geronimogonzalez/andino-jazzy/andino_description/docs/robot_rviz.png

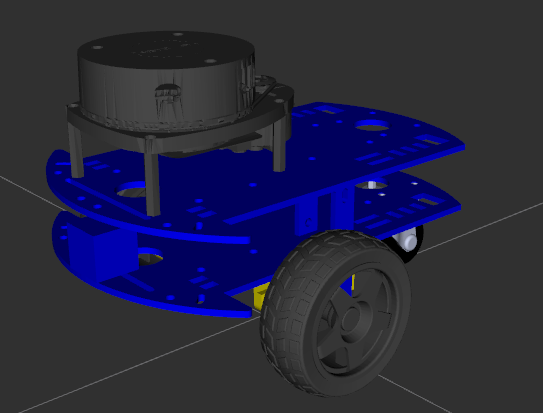
andino_description/docs/robot_rviz.png
