geronimogonzalez/andino-jazzy/navigation2/doc/requirements/images/Command-Pipeline-Support.png

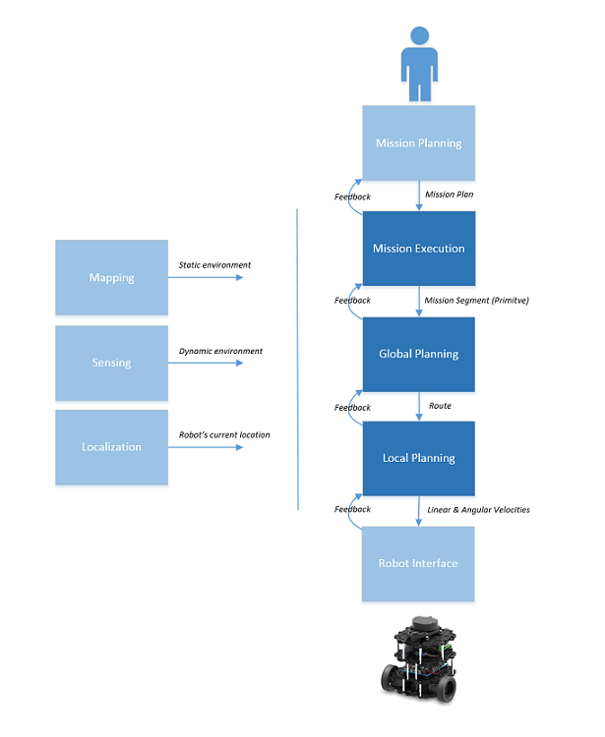
navigation2/doc/requirements/images/Command-Pipeline-Support.png
