geronimogonzalez/andino-jazzy/navigation2/doc/requirements/images/Context.png

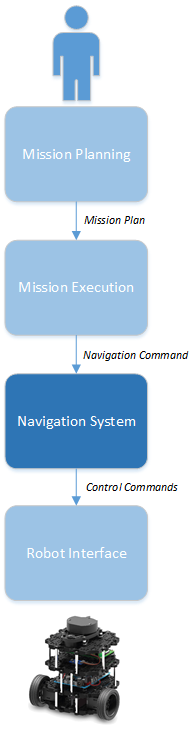
navigation2/doc/requirements/images/Context.png
