geronimogonzalez/andino-jazzy/navigation2/doc/requirements/images/Mapping-Use-Cases.png

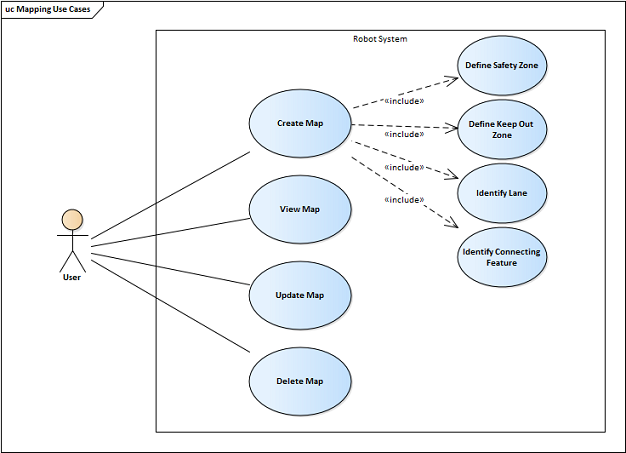
navigation2/doc/requirements/images/Mapping-Use-Cases.png
