geronimogonzalez/andino-jazzy/navigation2/doc/requirements/images/With-Support-Modules.png

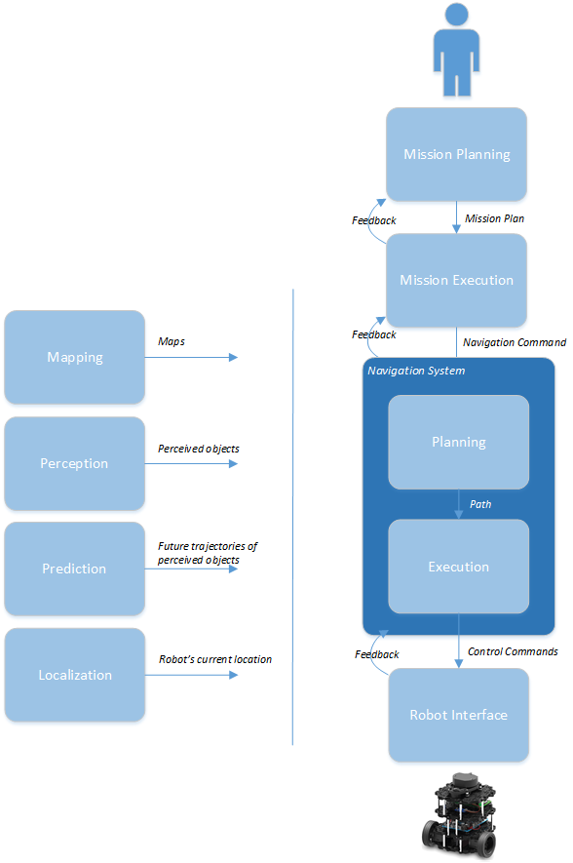
navigation2/doc/requirements/images/With-Support-Modules.png
