geronimogonzalez/andino-jazzy/navigation2/doc/sponsors_feb_2024.png

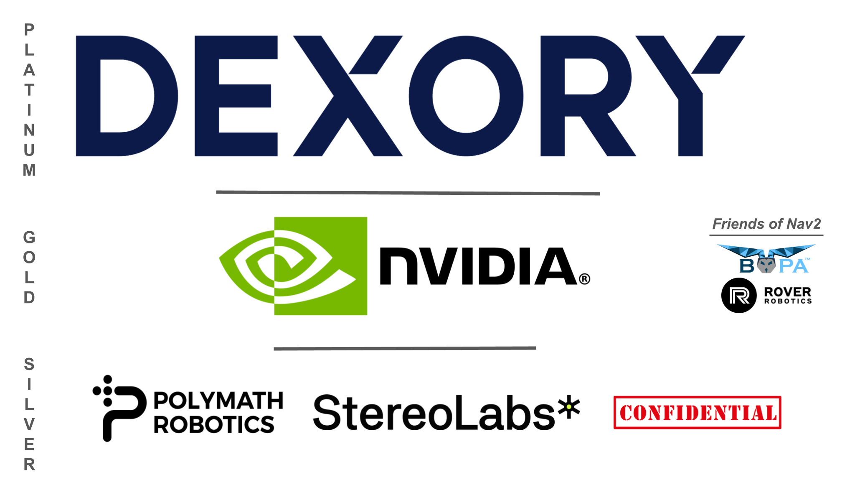
navigation2/doc/sponsors_feb_2024.png
