geronimogonzalez/andino-jazzy/navigation2/doc/sponsors_jan_2024.png

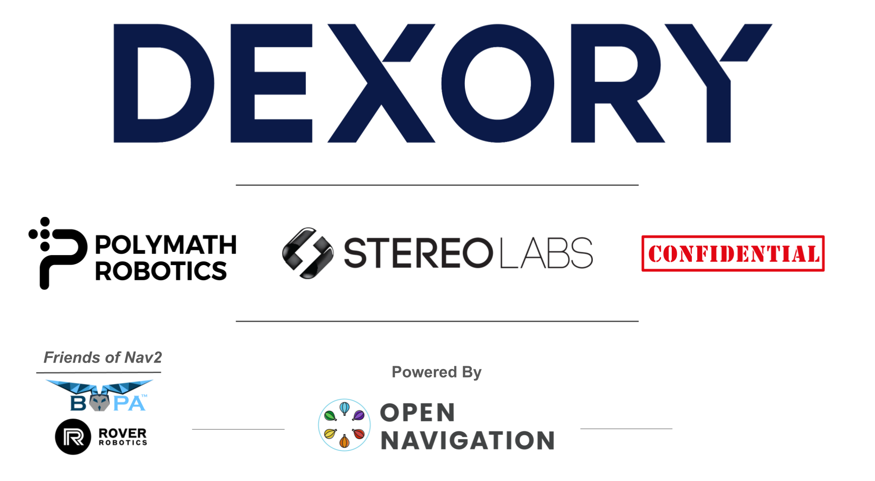
navigation2/doc/sponsors_jan_2024.png
