geronimogonzalez/andino-jazzy/navigation2/doc/sponsors_may_2023.png

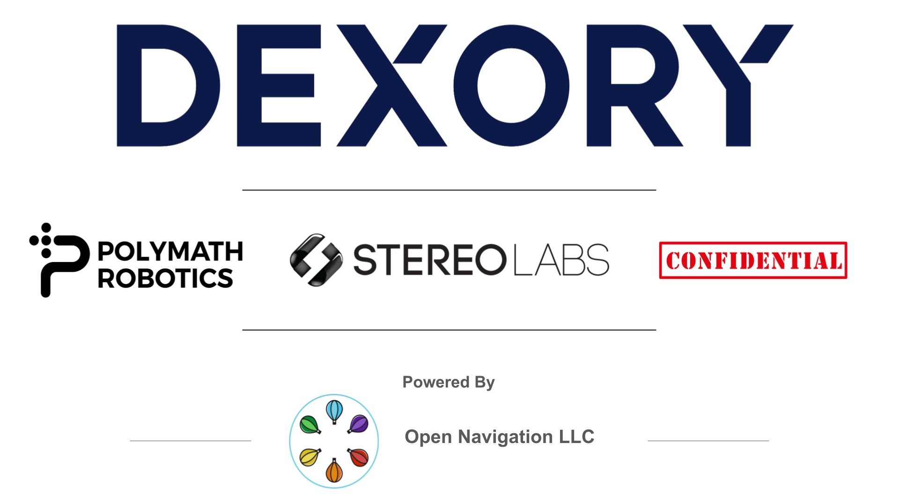
navigation2/doc/sponsors_may_2023.png
