geronimogonzalez/andino-jazzy/navigation2/nav2_bt_navigator/doc/follow_point.png

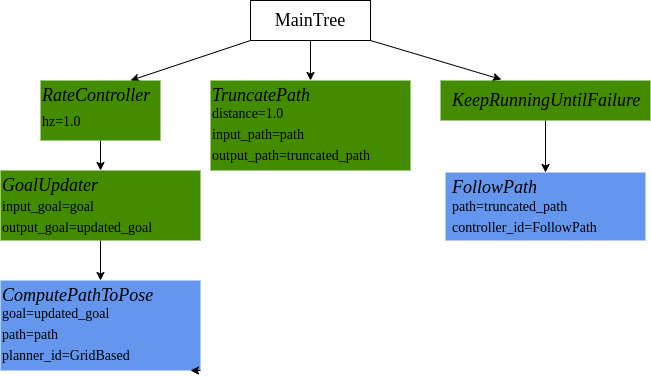
navigation2/nav2_bt_navigator/doc/follow_point.png
