geronimogonzalez/andino-jazzy/navigation2/nav2_bt_navigator/doc/legend.png

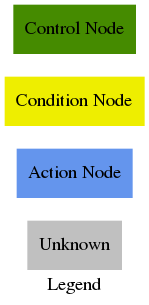
navigation2/nav2_bt_navigator/doc/legend.png
