geronimogonzalez/andino-jazzy/navigation2/nav2_bt_navigator/doc/navigate_w_replanning_distance.png

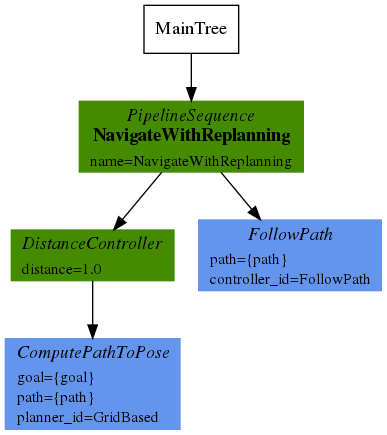
navigation2/nav2_bt_navigator/doc/navigate_w_replanning_distance.png
