geronimogonzalez/andino-jazzy/navigation2/nav2_bt_navigator/doc/parallel_w_goal_patience_and_recovery.png

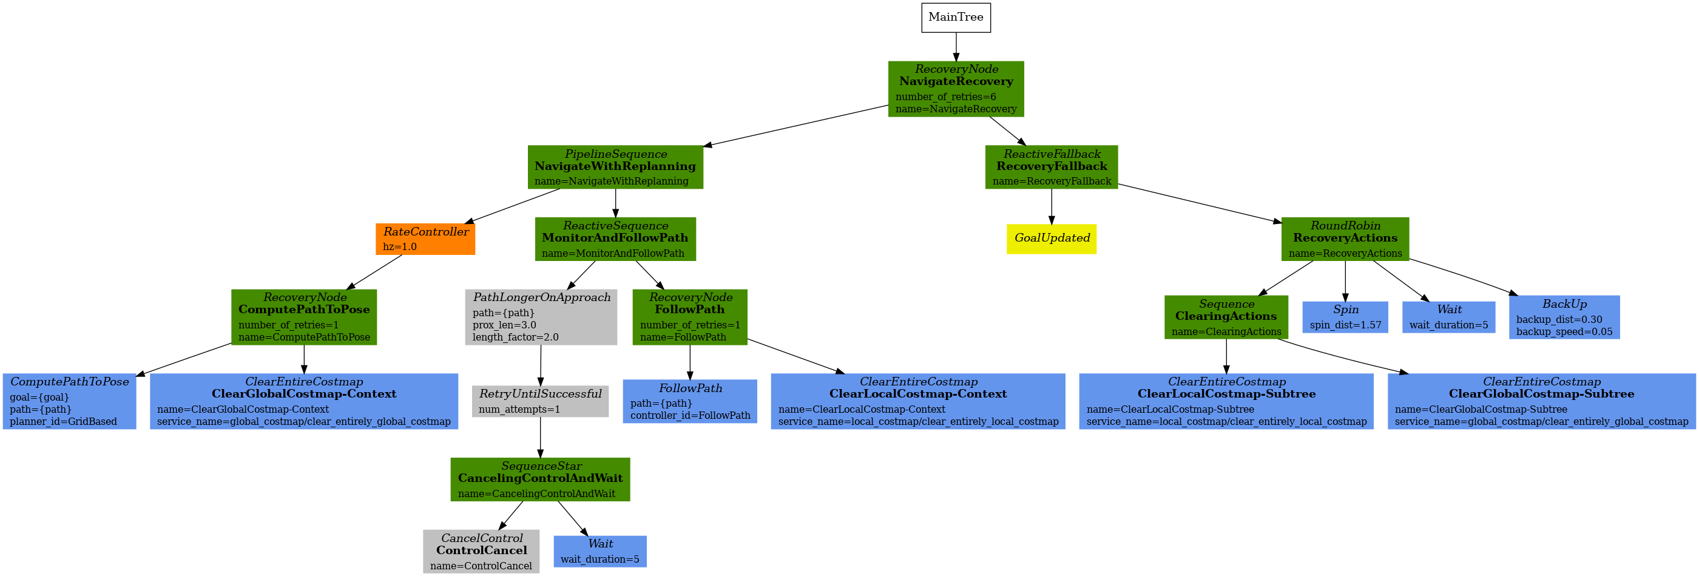
navigation2/nav2_bt_navigator/doc/parallel_w_goal_patience_and_recovery.png
