geronimogonzalez/andino-jazzy/navigation2/nav2_bt_navigator/doc/parallel_w_recovery.png

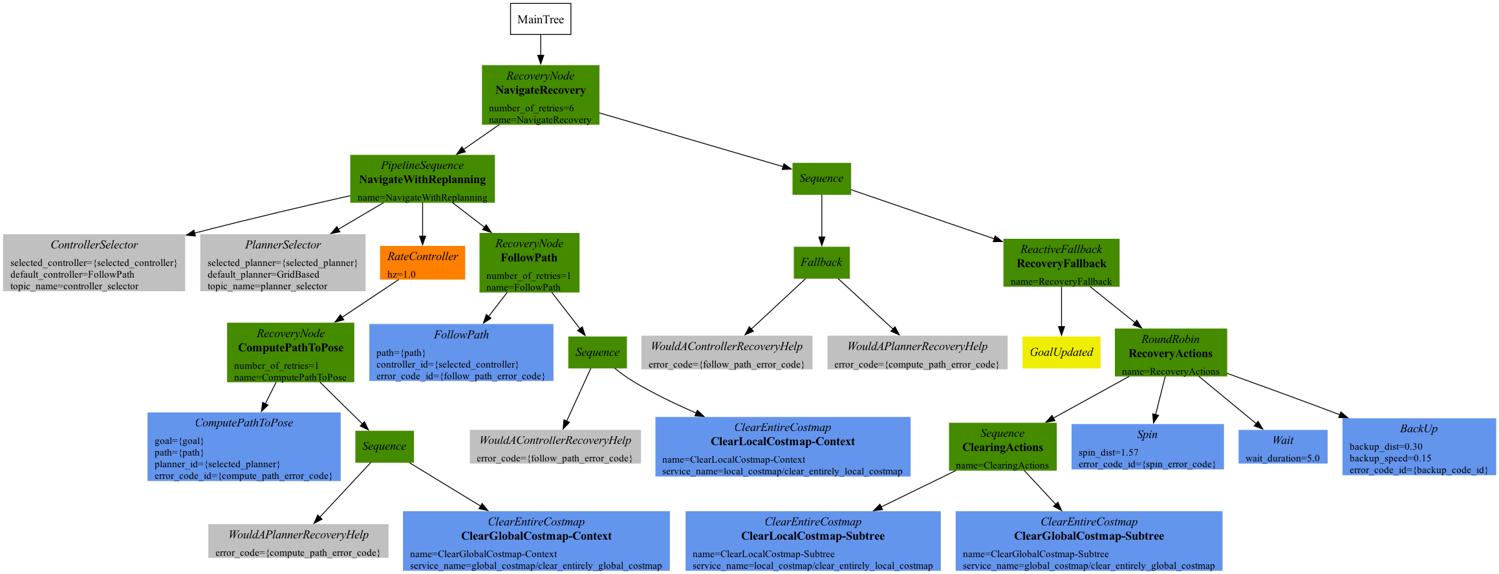
navigation2/nav2_bt_navigator/doc/parallel_w_recovery.png
