geronimogonzalez/andino-jazzy/navigation2/nav2_bt_navigator/doc/recovery_node.png

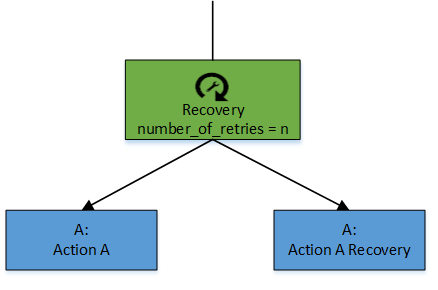
navigation2/nav2_bt_navigator/doc/recovery_node.png
