geronimogonzalez/andino-jazzy/navigation2/nav2_bt_navigator/doc/recovery_w_goal_updated.png

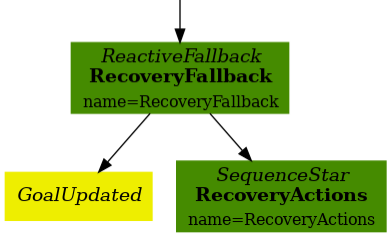
navigation2/nav2_bt_navigator/doc/recovery_w_goal_updated.png
