geronimogonzalez/andino-jazzy/navigation2/nav2_collision_monitor/doc/cm_ros_devday.png

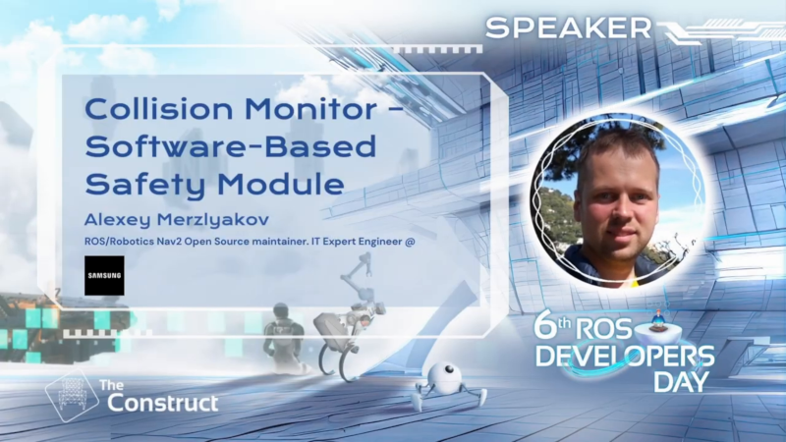
navigation2/nav2_collision_monitor/doc/cm_ros_devday.png
