geronimogonzalez/andino-jazzy/navigation2/nav2_collision_monitor/doc/HLD.png

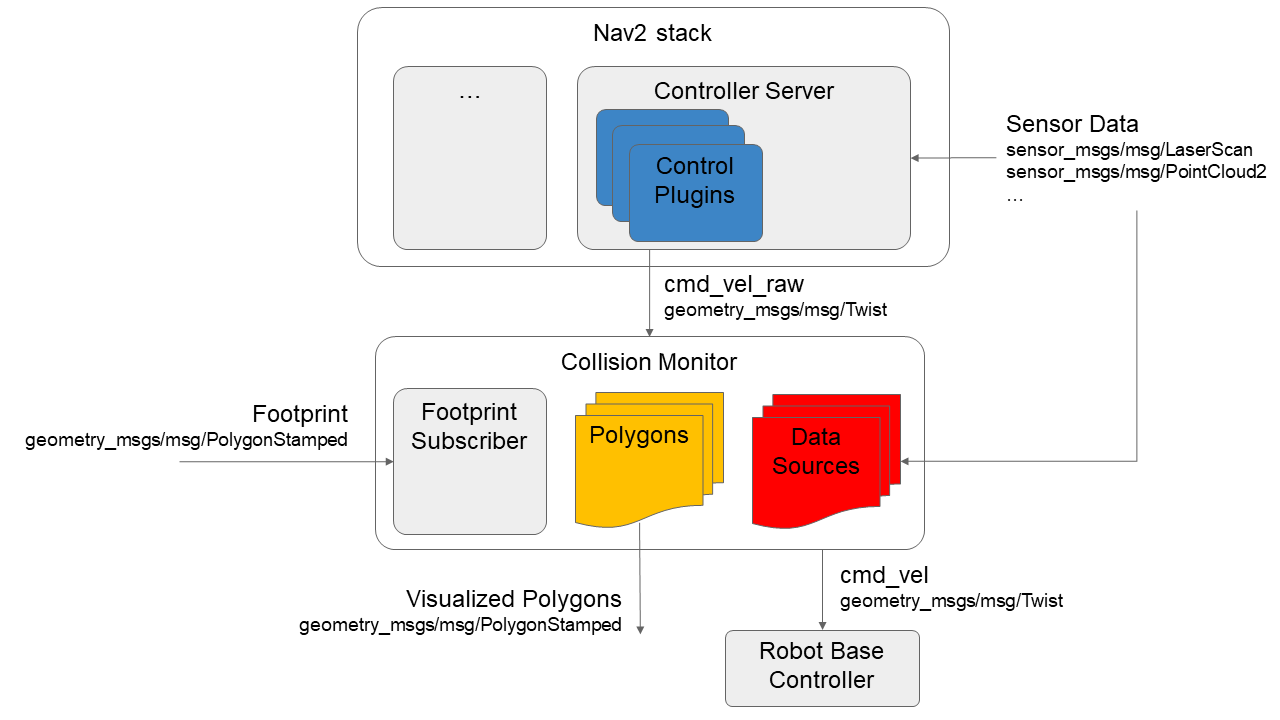
navigation2/nav2_collision_monitor/doc/HLD.png
