geronimogonzalez/andino-jazzy/navigation2/nav2_collision_monitor/doc/polygons.png

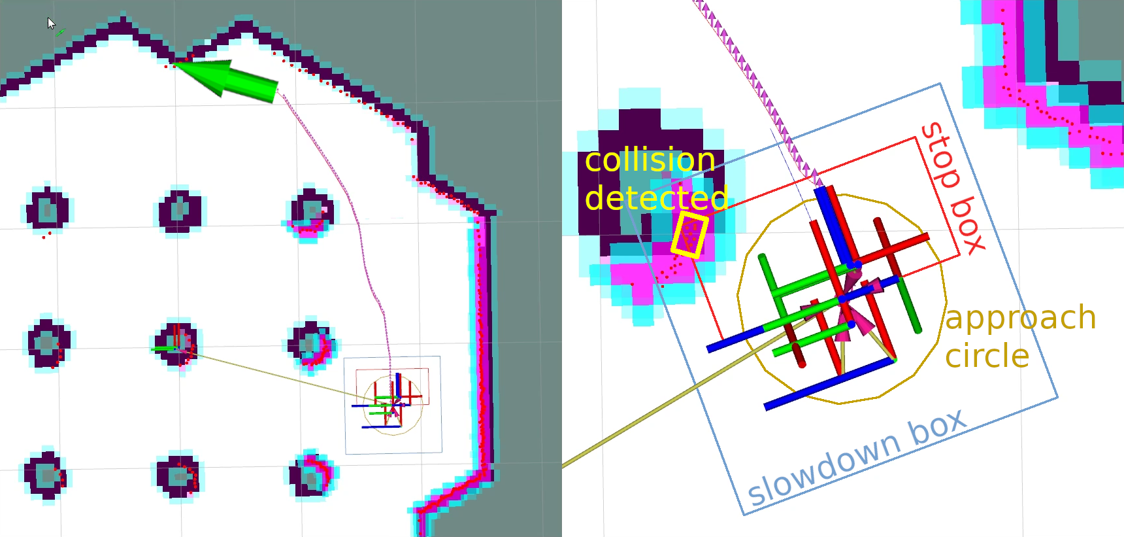
navigation2/nav2_collision_monitor/doc/polygons.png
