geronimogonzalez/andino-jazzy/navigation2/nav2_docking/docs/nv_on.png

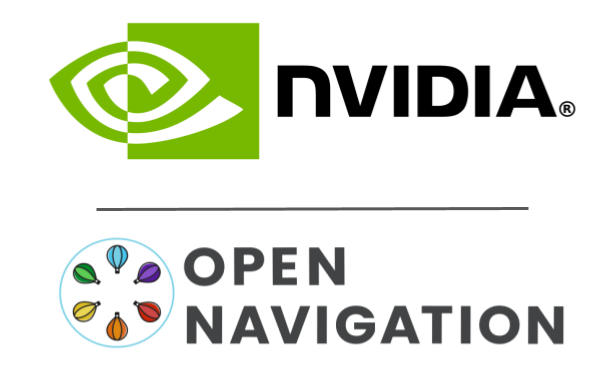
navigation2/nav2_docking/docs/nv_on.png
