geronimogonzalez/andino-jazzy/navigation2/nav2_graceful_controller/doc/trajectories.png

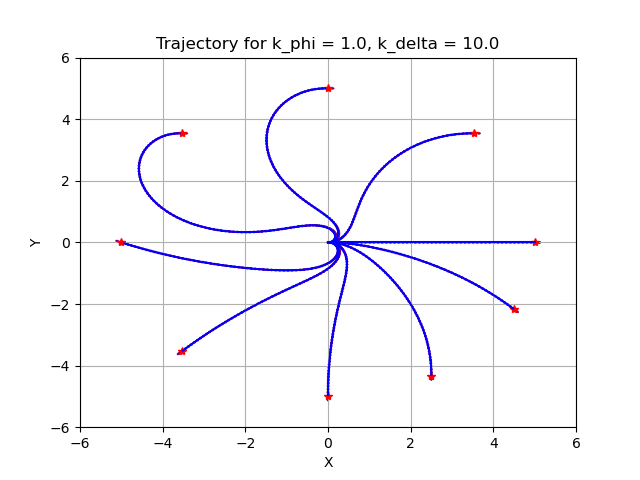
navigation2/nav2_graceful_controller/doc/trajectories.png
