geronimogonzalez/andino-jazzy/navigation2/nav2_lifecycle_manager/doc/uml_lifecycle_manager.JPG

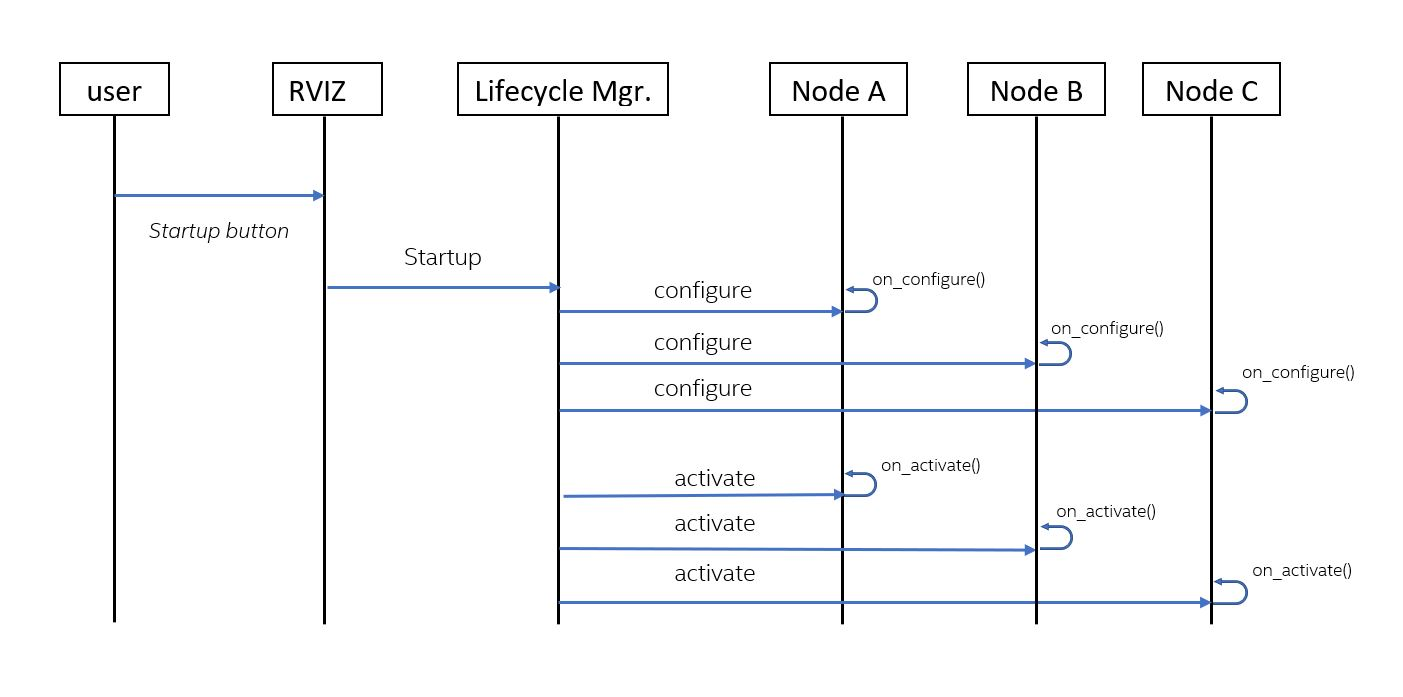
navigation2/nav2_lifecycle_manager/doc/uml_lifecycle_manager.JPG
