geronimogonzalez/andino-jazzy/navigation2/nav2_regulated_pure_pursuit_controller/doc/lookahead_algorithm.png

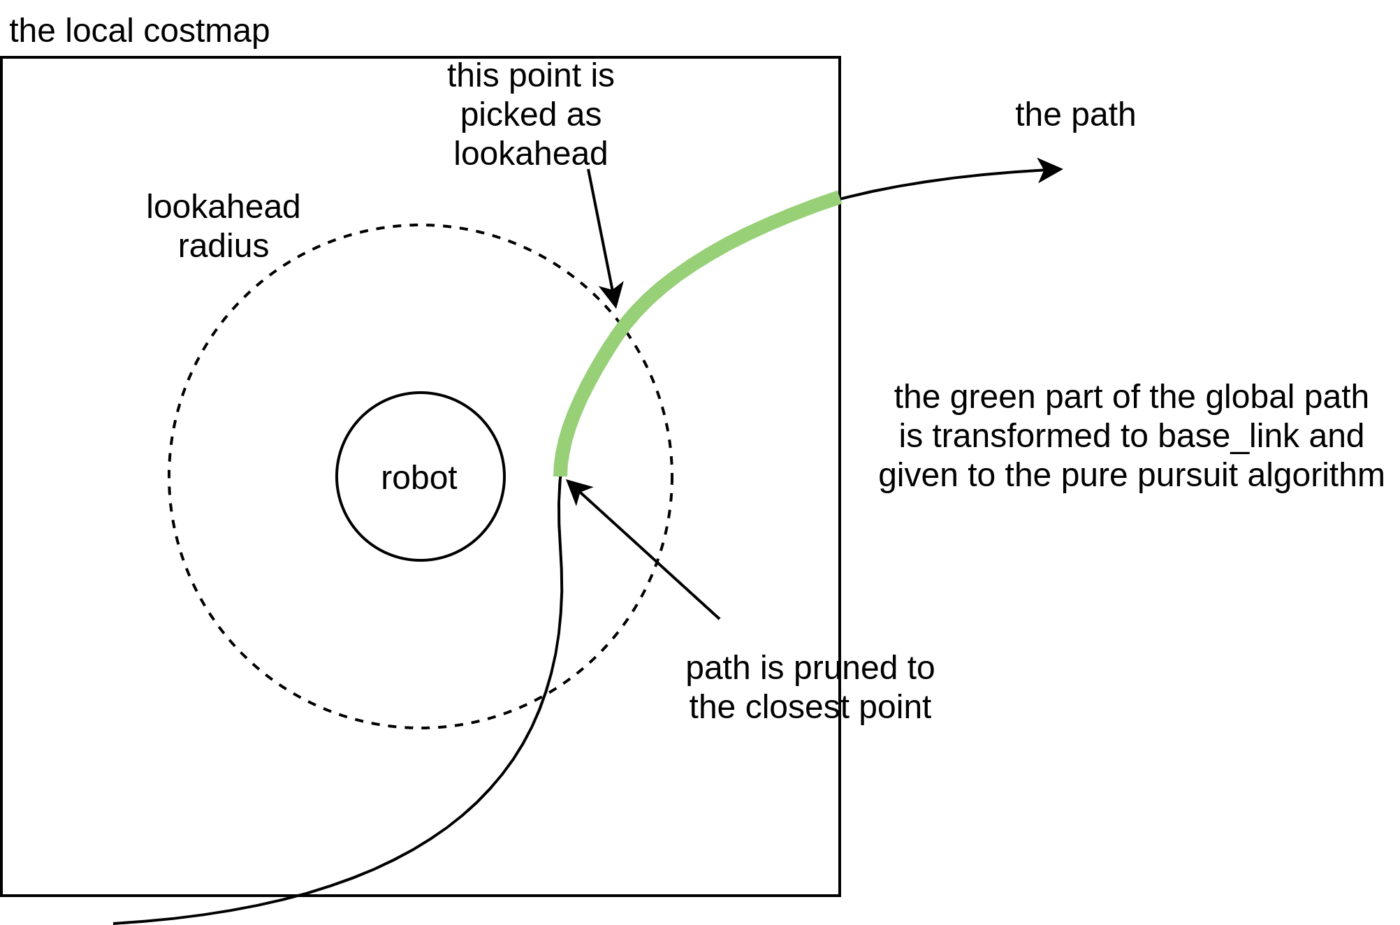
navigation2/nav2_regulated_pure_pursuit_controller/doc/lookahead_algorithm.png
