geronimogonzalez/andino-jazzy/navigation2/nav2_smac_planner/lattice_primitives/docs/all_trajectories.png

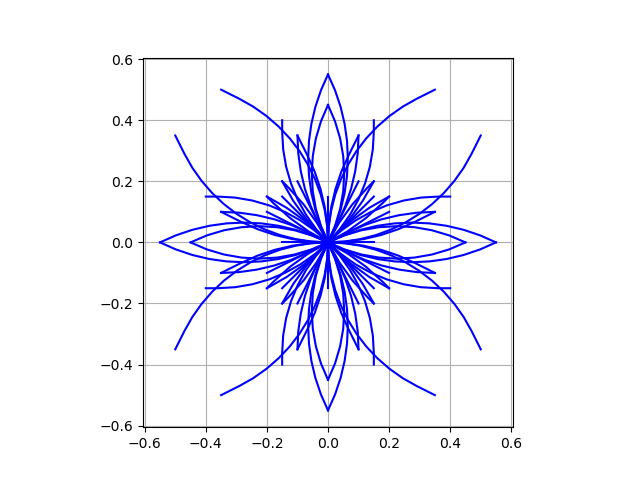
navigation2/nav2_smac_planner/lattice_primitives/docs/all_trajectories.png
