geronimogonzalez/andino-jazzy/navigation2/nav2_smac_planner/lattice_primitives/docs/angle_discretization.png

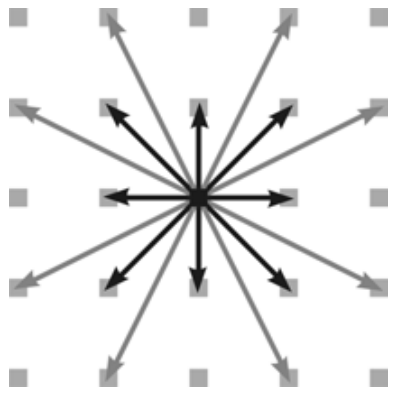
navigation2/nav2_smac_planner/lattice_primitives/docs/angle_discretization.png
