geronimogonzalez/andino-jazzy/navigation2/nav2_smac_planner/lattice_primitives/sample_primitives/5cm_resolution/1m_turning_radius/all_trajectories.png

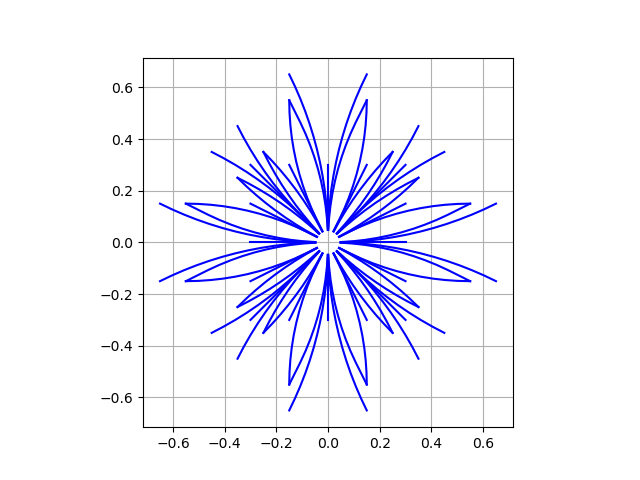
navigation2/nav2_smac_planner/lattice_primitives/sample_primitives/5cm_resolution/1m_turning_radius/all_trajectories.png
