geronimogonzalez/andino-jazzy/navigation2/nav2_smac_planner/media/A.png

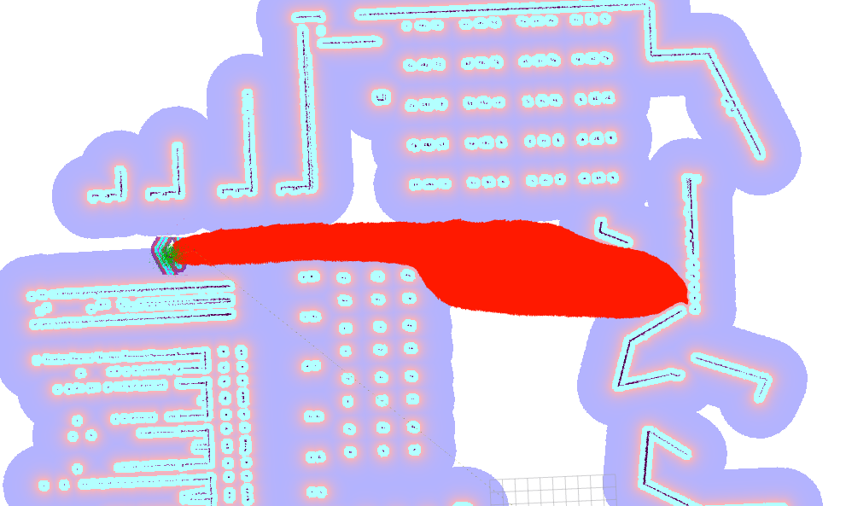
navigation2/nav2_smac_planner/media/A.png
