geronimogonzalez/andino-jazzy/navigation2/nav2_smac_planner/media/B.png

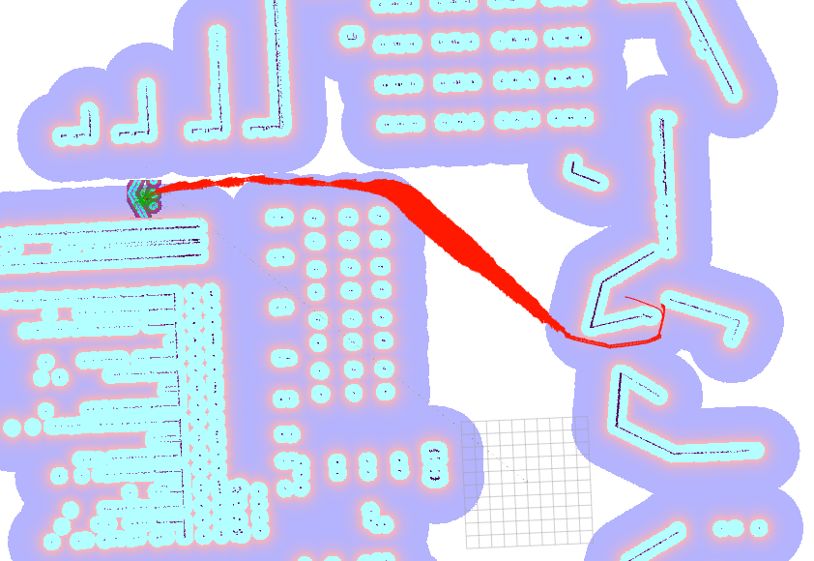
navigation2/nav2_smac_planner/media/B.png
