geronimogonzalez/andino-jazzy/navigation2/nav2_theta_star_planner/img/00-37.png

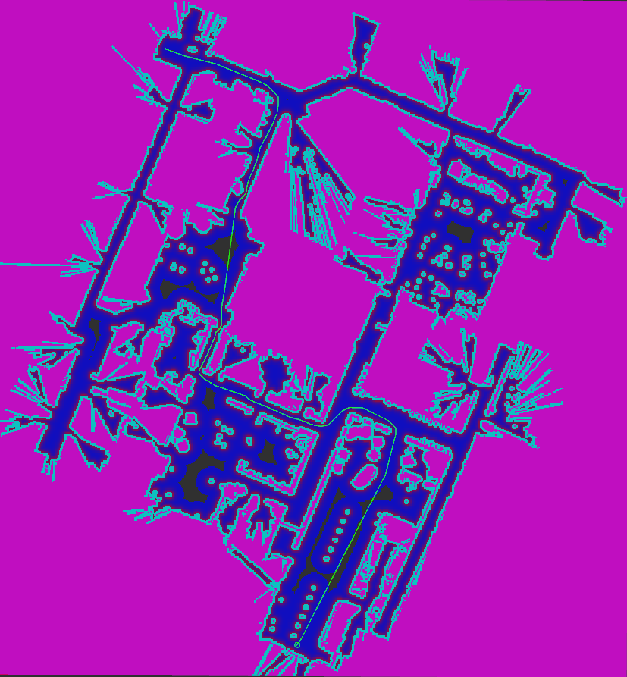
navigation2/nav2_theta_star_planner/img/00-37.png
