geronimogonzalez/andino-jazzy/andino_description/meshes/andino/chassis.stl

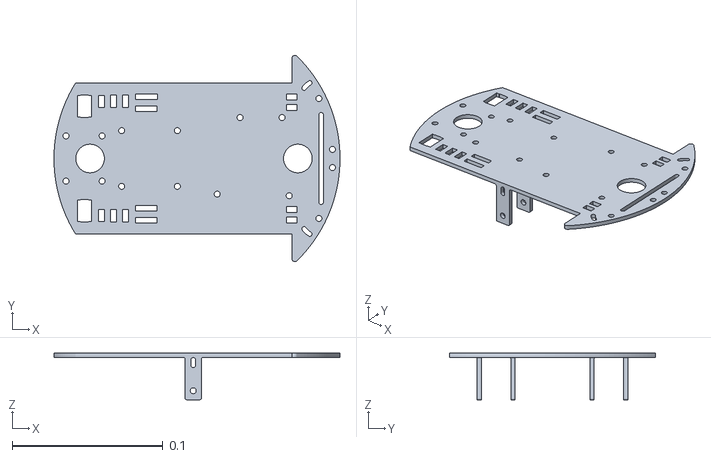
[picture p65: CAD file, 2025-10-09]
andino_description/meshes/andino/chassis.stl
0.19 x 0.137 x 0.0309
