geronimogonzalez/andino-jazzy/andino_description/meshes/andino/caster_wheel.stl

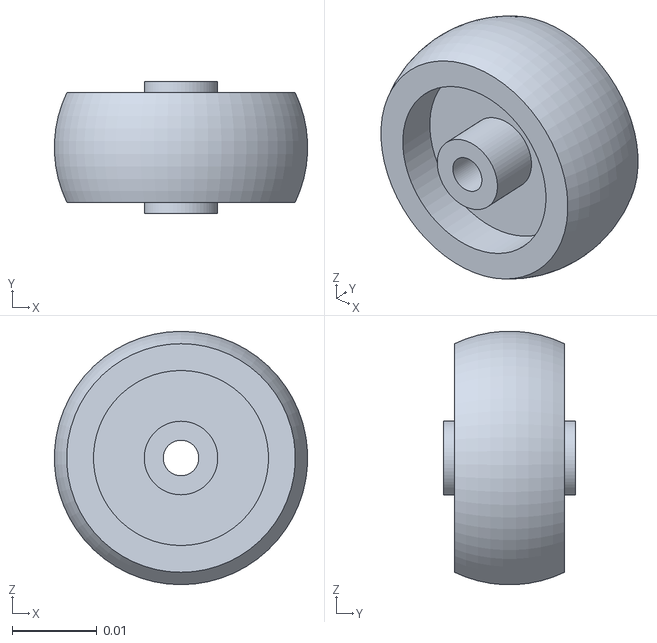
[picture p66: CAD file, 2025-10-09]
andino_description/meshes/andino/caster_wheel.stl
0.0299 x 0.0156 x 0.03
