geronimogonzalez/andino-jazzy/navigation2/nav2_costmap_2d/test/unit/keepout_filter_test.jpg

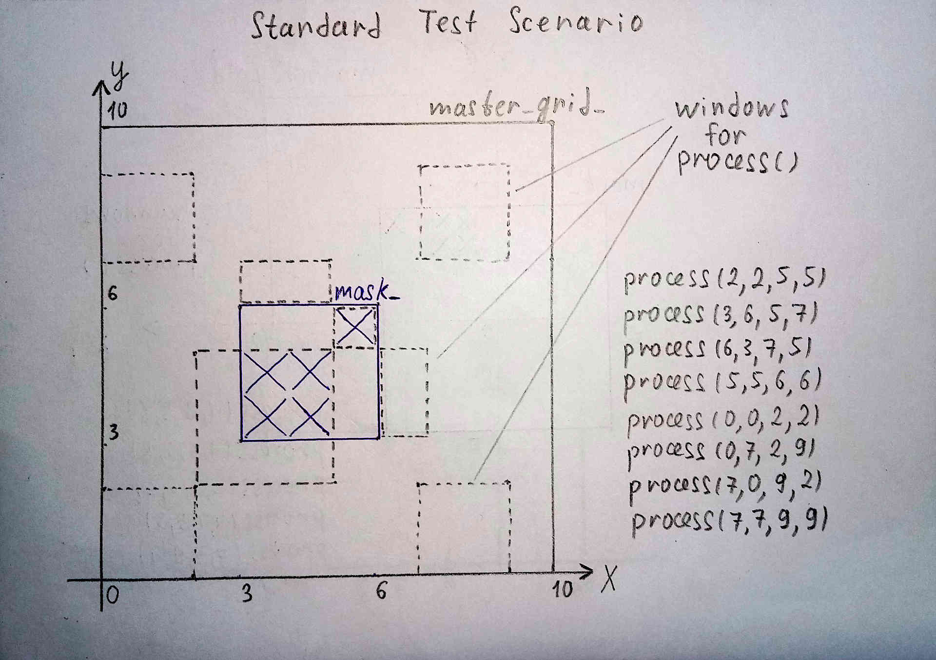
navigation2/nav2_costmap_2d/test/unit/keepout_filter_test.jpg
