geronimogonzalez/andino-jazzy/navigation2/nav2_smac_planner/test/3planners.png

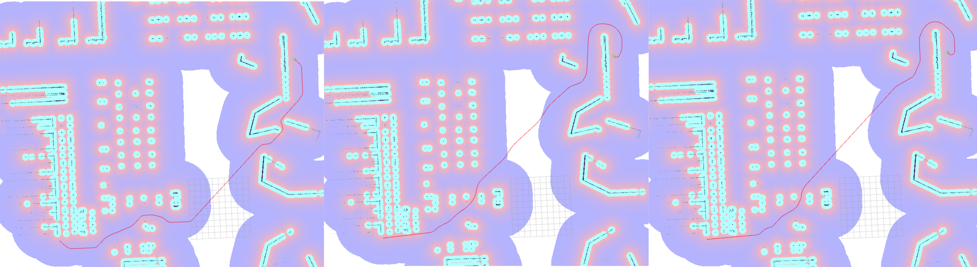
navigation2/nav2_smac_planner/test/3planners.png
