geronimogonzalez/andino-jazzy/navigation2/nav2_smac_planner/test/path.png

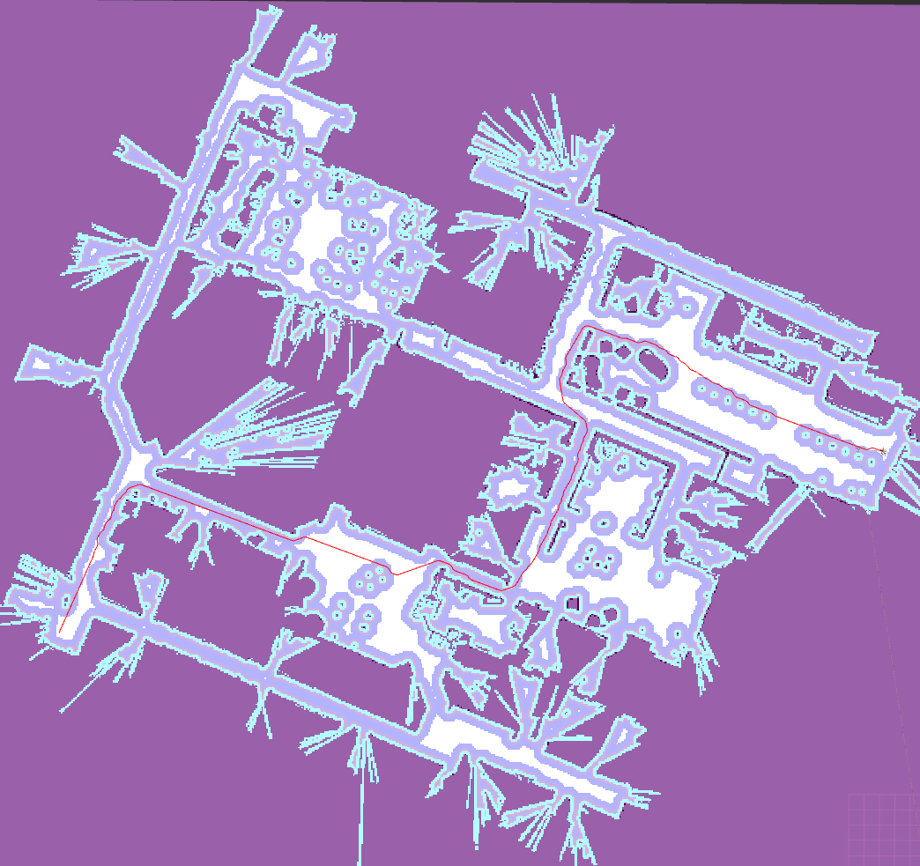
navigation2/nav2_smac_planner/test/path.png
