geronimogonzalez/andino-jazzy/navigation2/nav2_system_tests/maps/empty_room.png

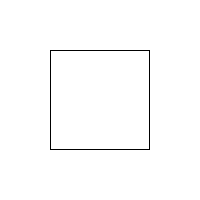
navigation2/nav2_system_tests/maps/empty_room.png
