geronimogonzalez/andino-jazzy/navigation2/nav2_system_tests/src/costmap_filters/keepout_plan.png

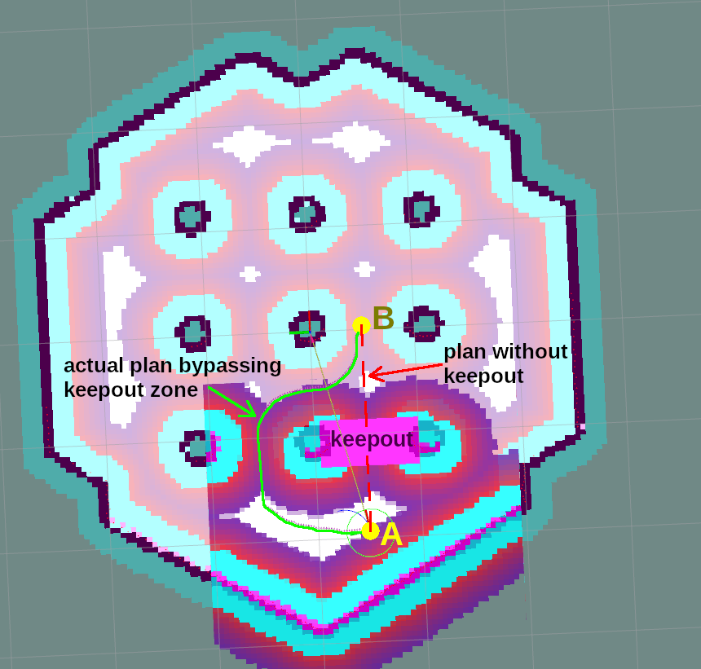
navigation2/nav2_system_tests/src/costmap_filters/keepout_plan.png
