geronimogonzalez/andino-jazzy/navigation2/nav2_system_tests/src/planning/example_result.png

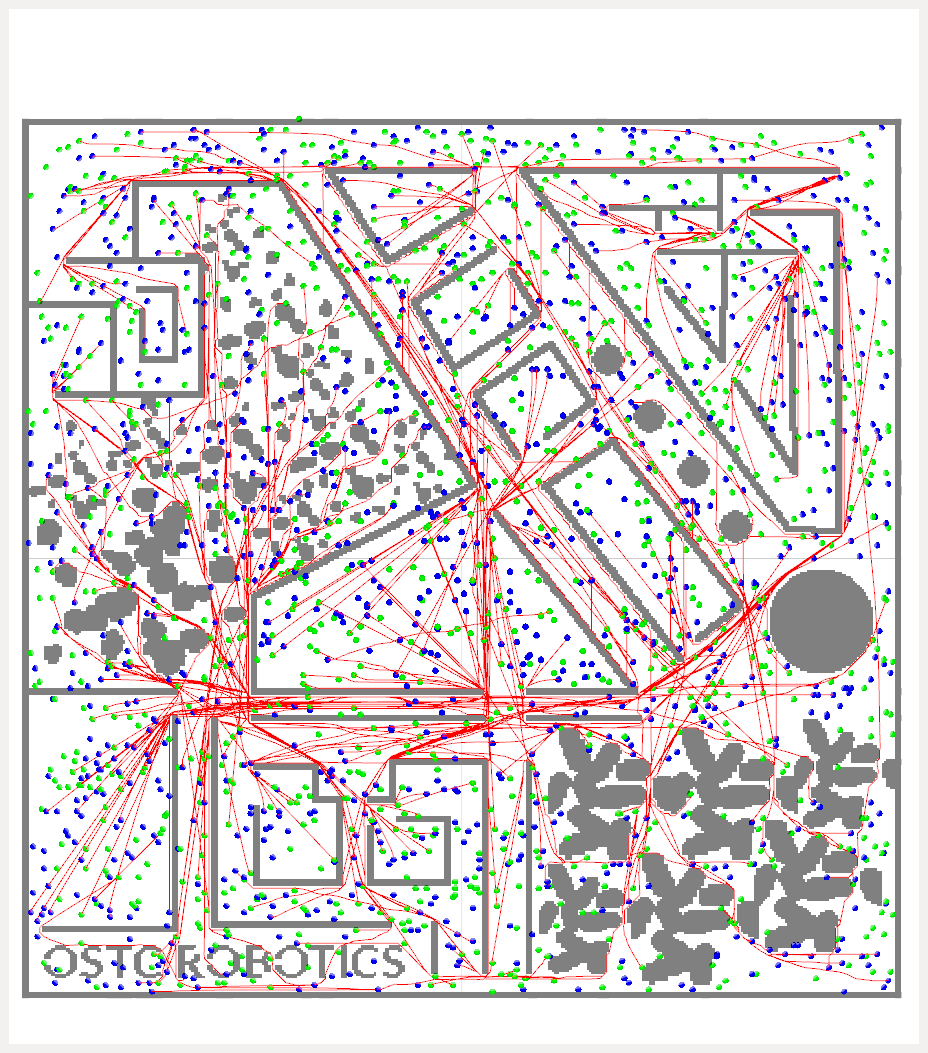
navigation2/nav2_system_tests/src/planning/example_result.png
